xxpESP32/Pen/字库/lvglFontTool_Set.jpg

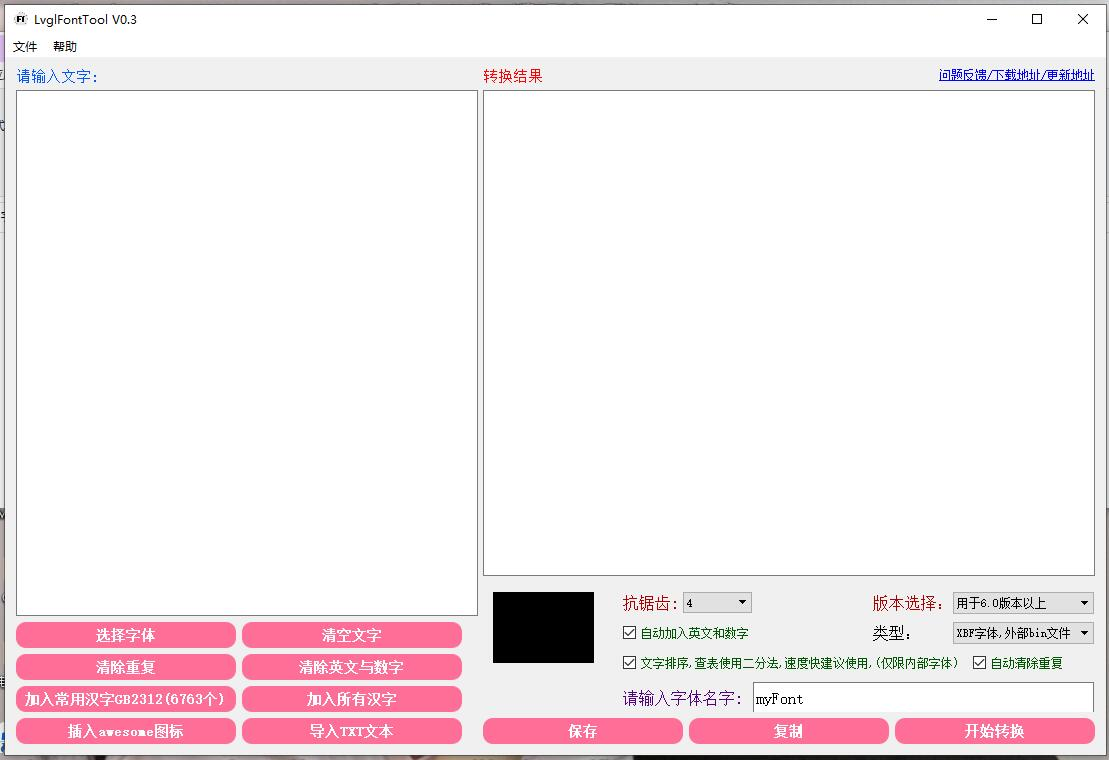
字库/lvglFontTool_Set.jpg
