xxpESP32/Pen/硬件电路/PCB图.png

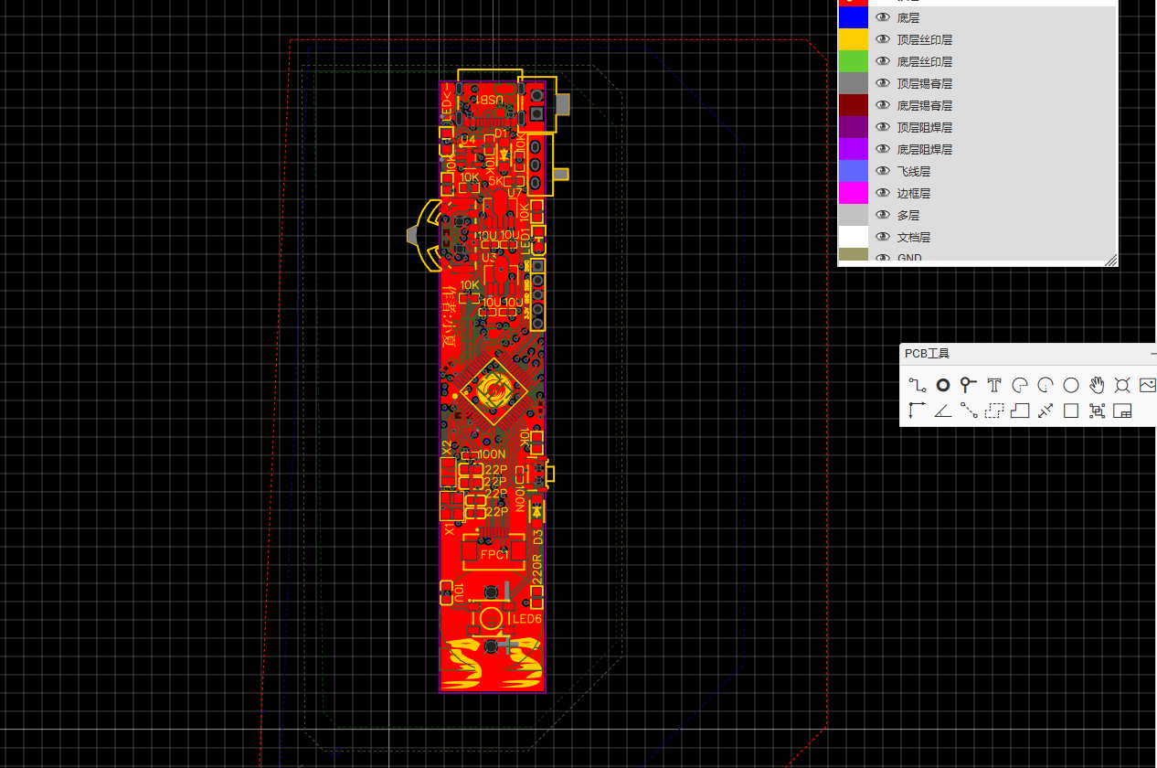
硬件电路/PCB图.png
