xxpESP32/Pen/硬件电路/电路原理图.png

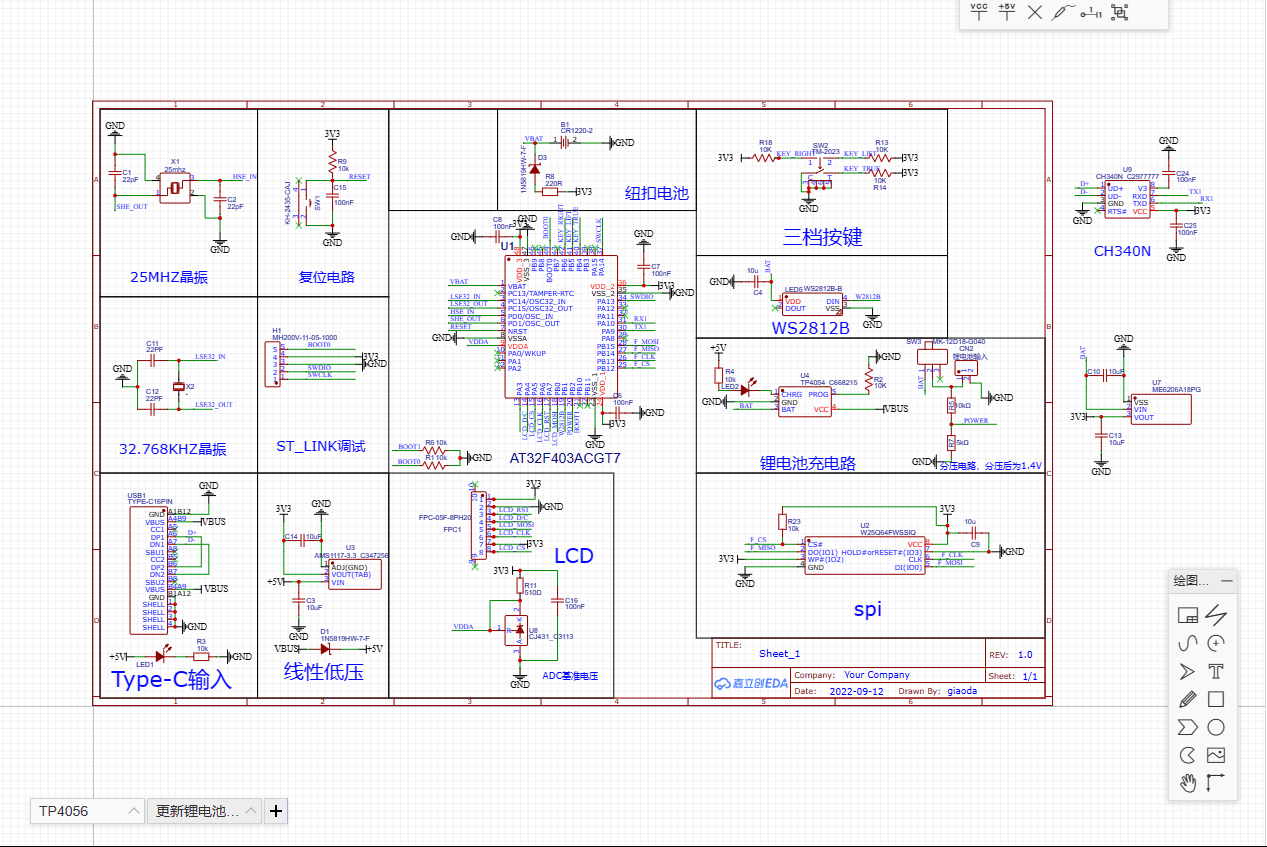
硬件电路/电路原理图.png
