xxpESP32/Pen/智能笔_UG/UI/NOW_STL/TOP.stl

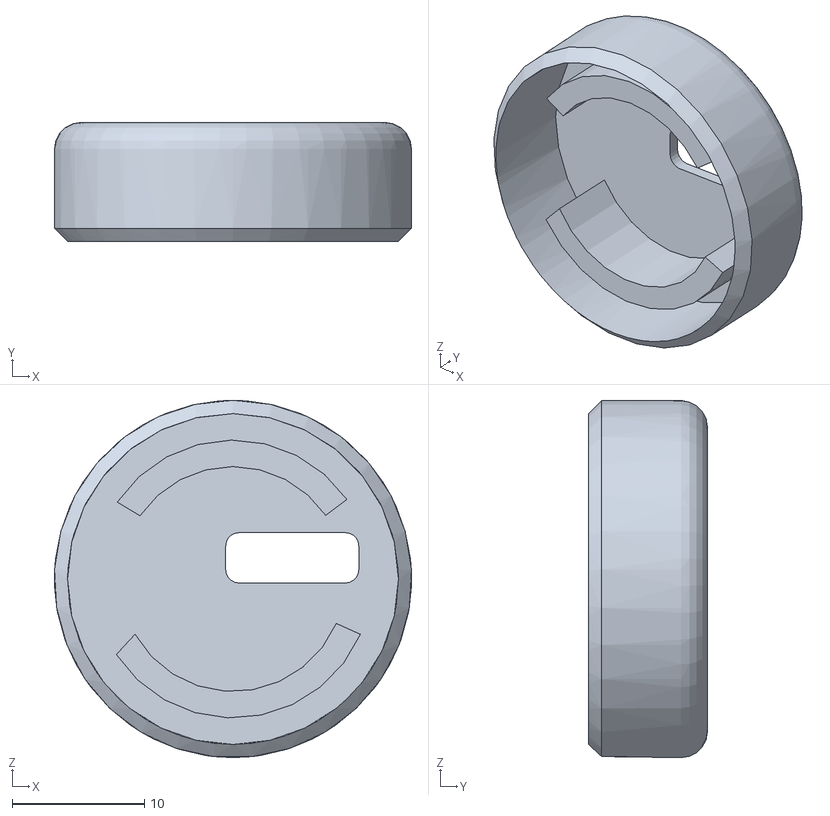
[picture p19: CAD file, 2023-03-08]
智能笔_UG/UI/NOW_STL/TOP.stl
27.0 x 9.00 x 27.0
