xxpESP32/Pen/智能笔_UG/UI/NOW_STL/BOTTON.stl

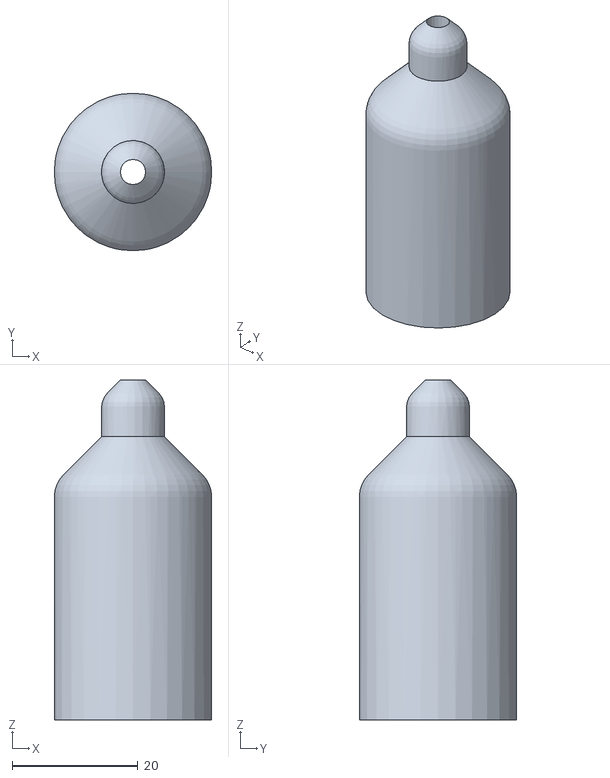
[picture p20: CAD file, 2023-03-08]
智能笔_UG/UI/NOW_STL/BOTTON.stl
25.0 x 25.0 x 54.0
