xxpESP32/Pen/智能笔_UG/UI/NOW_STL/BOTTON_N.stl

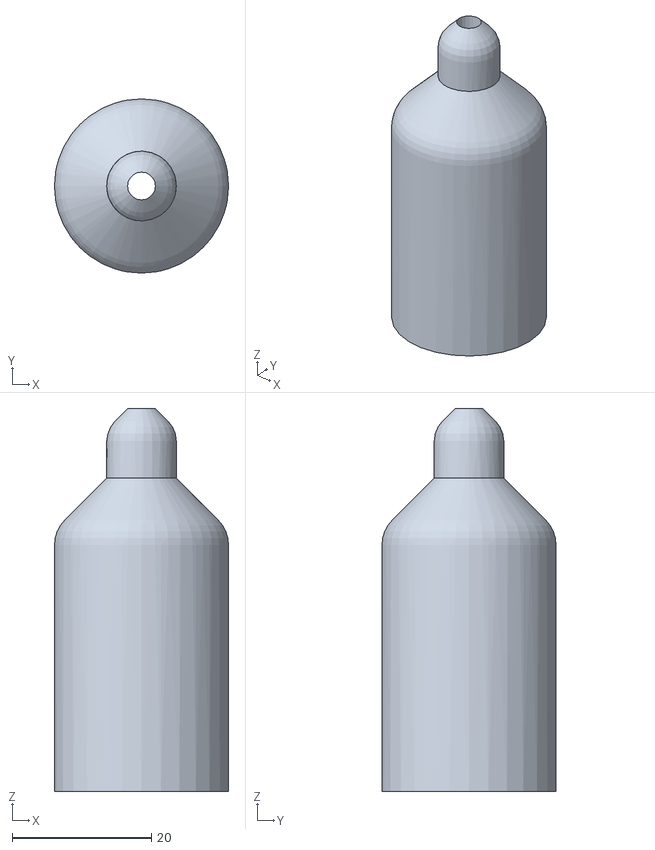
[picture p21: CAD file, 2023-03-08]
智能笔_UG/UI/NOW_STL/BOTTON_N.stl
25.0 x 25.0 x 55.0
