xxpESP32/Pen/程序源码/mdk_v5_Pen_must/GUI/lvgl_driver/lv_port_disp.h

/**
 * @file lv_port_disp.h
 *
 */

 /*Copy this file as "lv_port_disp.h" and set this value to "1" to enable content*/
#if 1

#ifndef LV_PORT_DISP_H
#define LV_PORT_DISP_H

#ifdef __cplusplus
extern "C" {
#endif

/*********************
 *      INCLUDES
 *********************/
#include "lvgl/lvgl.h"

/*********************
 *      DEFINES
 *********************/

/**********************
 *      TYPEDEFS
 **********************/

/**********************
 * GLOBAL PROTOTYPES
 **********************/

/**********************
 *      MACROS
 **********************/
void lv_port_disp_init(void);
#ifdef __cplusplus
} /* extern "C" */
#endif

#endif /*LV_PORT_DISP_H*/

#endif /*Disable/Enable content*/
