xxpESP32/Pen/程序源码/mdk_v5_Pen_must/GUI/lvgl_driver/lv_port_indev.h

/**
 * @file lv_port_indev.h
 *
 */

 /*Copy this file as "lv_port_indev.h" and set this value to "1" to enable content*/
#if 1

#ifndef LV_PORT_INDEV_H
#define LV_PORT_INDEV_H

#ifdef __cplusplus
extern "C" {
#endif

/*********************
 *      INCLUDES
 *********************/
#include "lvgl/lvgl.h"

/*********************
 *      DEFINES
 *********************/

/**********************
 *      TYPEDEFS
 **********************/

/**********************
 * GLOBAL PROTOTYPES
 **********************/

/**********************
 *      MACROS
 **********************/
extern lv_indev_t * indev_ecodes;
void lv_port_indev_init(void);

#ifdef __cplusplus
} /* extern "C" */
#endif

#endif /*LV_PORT_INDEV_TEMPL_H*/

#endif /*Disable/Enable content*/
